PUT-Motorsport/PUTM_DV_ASB/hardware/44_pressure-gauge.bf32485a09.png

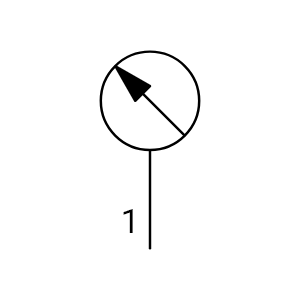
hardware/44_pressure-gauge.bf32485a09.png
