PUT-Motorsport/PUTM_DV_ASB/hardware/supervisor.png

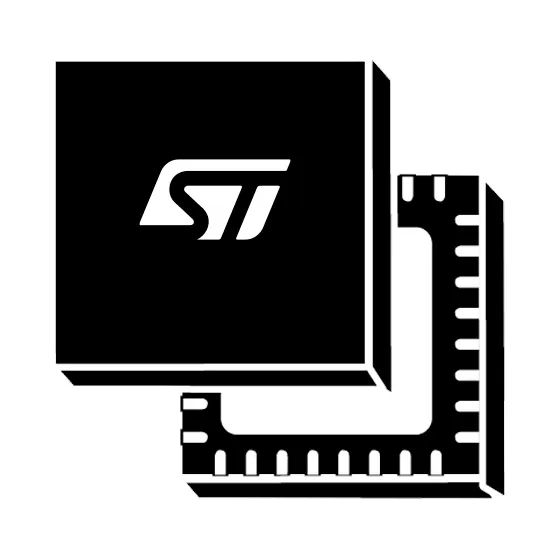
hardware/supervisor.png
