PUT-Motorsport/PUTM_DV_ASB/roznice_f103_l4.png

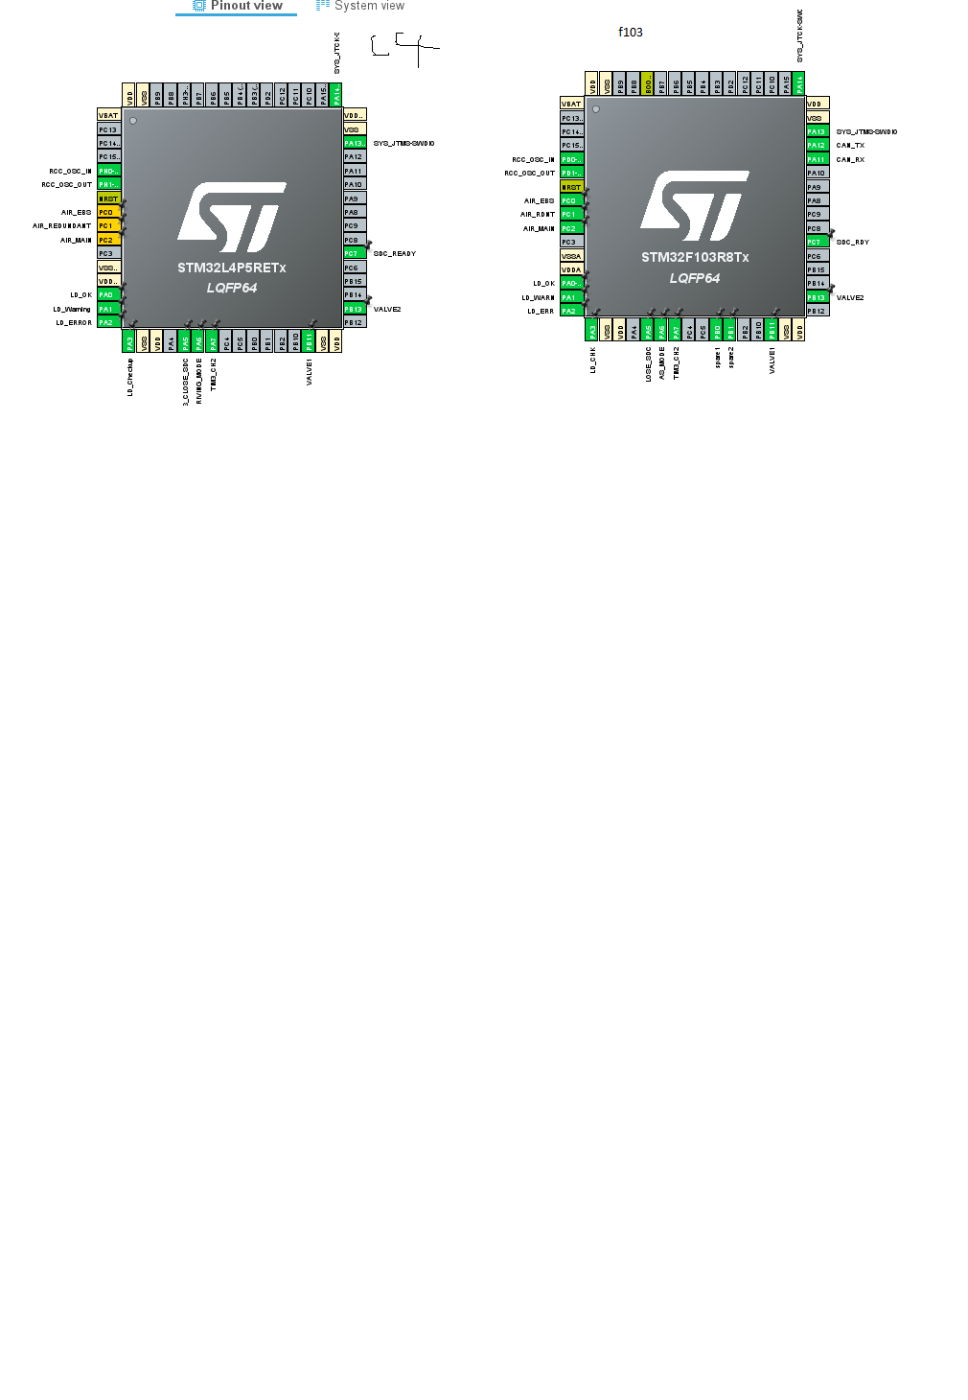
roznice_f103_l4.png
