PUT-Motorsport/PUTM_DV_ASB/SCSdiag.png

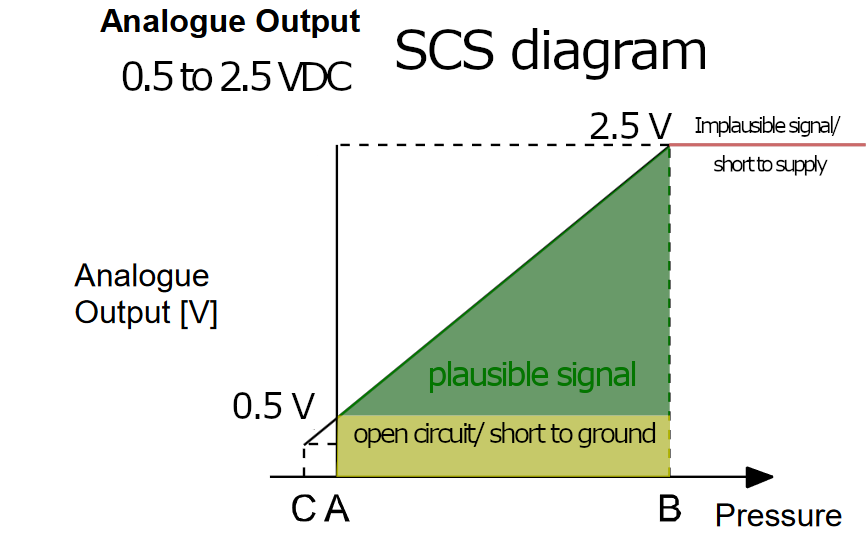
SCSdiag.png
