PUT-Motorsport/PUTM_DV_ASB/solenoidcontrol.bmp

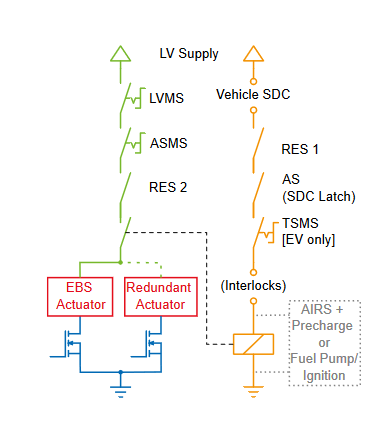
solenoidcontrol.bmp
