PUT-Motorsport/PUTM_DV_ASB/SYM/Pressure_sensor_r2.asc

B1: bv; V=4+0.2*sin(100*314*time)
C1: cap; 10n
C2: cap; 10n
R1: res; 100k
R2: res; 200k
R3: res; 200k
R4: res; 100k
R5: res; 4.7k
U1: OPA365
U2: UDZV3_3B
V1: voltage; 3.3
V2: voltage; SINE(3.3 3.3 20); Rser=1k
V3: voltage; 5; Rser=1k
V4: voltage; 19
Named nets: 0, output, sensor, 3v3
cutoff=abt 150Hz (6.66ms)
.tran 200m
