PUT-Motorsport/PUTM_DV_ASB/SYM/EBS Logic.asc

C1: cap; 10n
C2: cap; 10n
C3: cap; 10n
D1: zener; MMBZ6V8ALY
D2: zener; MMBZ6V8ALY
D3: zener; MMBZ6V8ALY
R1: res; 22k
R2: res; 3k
R3: res; 22k
R4: res; 3k
R5: res; 22k
R6: res; 3k
U1: 74hc157; VCC=3.3  SPEED=1.0  TRIPDT=1e-9
U2: CD4081B; VDD=3.3  SPEED=1.0  TRIPDT=5e-9
U3: CD4081B; VDD=3.3V  SPEED=1.0  TRIPDT=5e-9
U4: CD4081B; VDD=3.3V  SPEED=1.0  TRIPDT=5e-9
U5: 74hc74; VCC=3.3  SPEED=1.0  TRIPDT=1e-9
U6: CD4011B; VDD=3.3  SPEED=1.0  TRIPDT=5e-9
U7: CD4071B; VDD=3.3  SPEED=1.0  TRIPDT=5e-9
U8: 74hc74; VCC=3.3  SPEED=1.0  TRIPDT=1e-9
V1: voltage; 3.3
V2: voltage; PULSE(0 3.3 50m 10m 10m 6)
V3: voltage; 24
V4: voltage; PULSE(0 3.3 0.5 0.00001 0.00001 100m 2 3)
Named nets: 0, SDC_RELAI, SDC_READY, WD_RESET, SAFETY_sense, WDO, TS_ON_COCKPIT1, TS_ON_EXT1, AS_DRIVING_MODE, SAFETY, TSON_EXT, TSON_DRV, RESET, HIGH, AS_CLOSE_SD
.tran 5
.include CD4000.lib
uC logic states
24V "Logic"
