PUT-Motorsport/PUTM_DV_ASB/SYM/Pressure_sensor.asc

C1: cap; 5.6n
R1: res; 1k
R2: res; 2k
R3: res; 1k
U2: MAX4238
V1: voltage; 5
V2: voltage; 1
Named nets: 0, +5, OUTPUT_SIG, input_sig
Linear characteristics of PSE540: 1V=0bar 5V=10bar -1bar=0,6V
;dc V2 1 5
.dc V2 1 5
